cloudymike/fermctrl/local/awsiotconfig.py

CERT_FILE = "cert"
KEY_FILE = "key"

#if you change the ClientId make sure update AWS policy
MQTT_CLIENT_ID = "esp32"

MQTT_PORT = "8883"

#if you change the topic make sure update AWS policy
MQTT_TOPIC = "tempctrlpub"

#Change the following to match your environment
MQTT_HOST = "a2d09uxsvr5exq-ats.iot.us-west-2.amazonaws.com"
